aliaydin96/EngineeringDesign/Completed/Business Statement Report/CV's/NailTosunCV.pdf

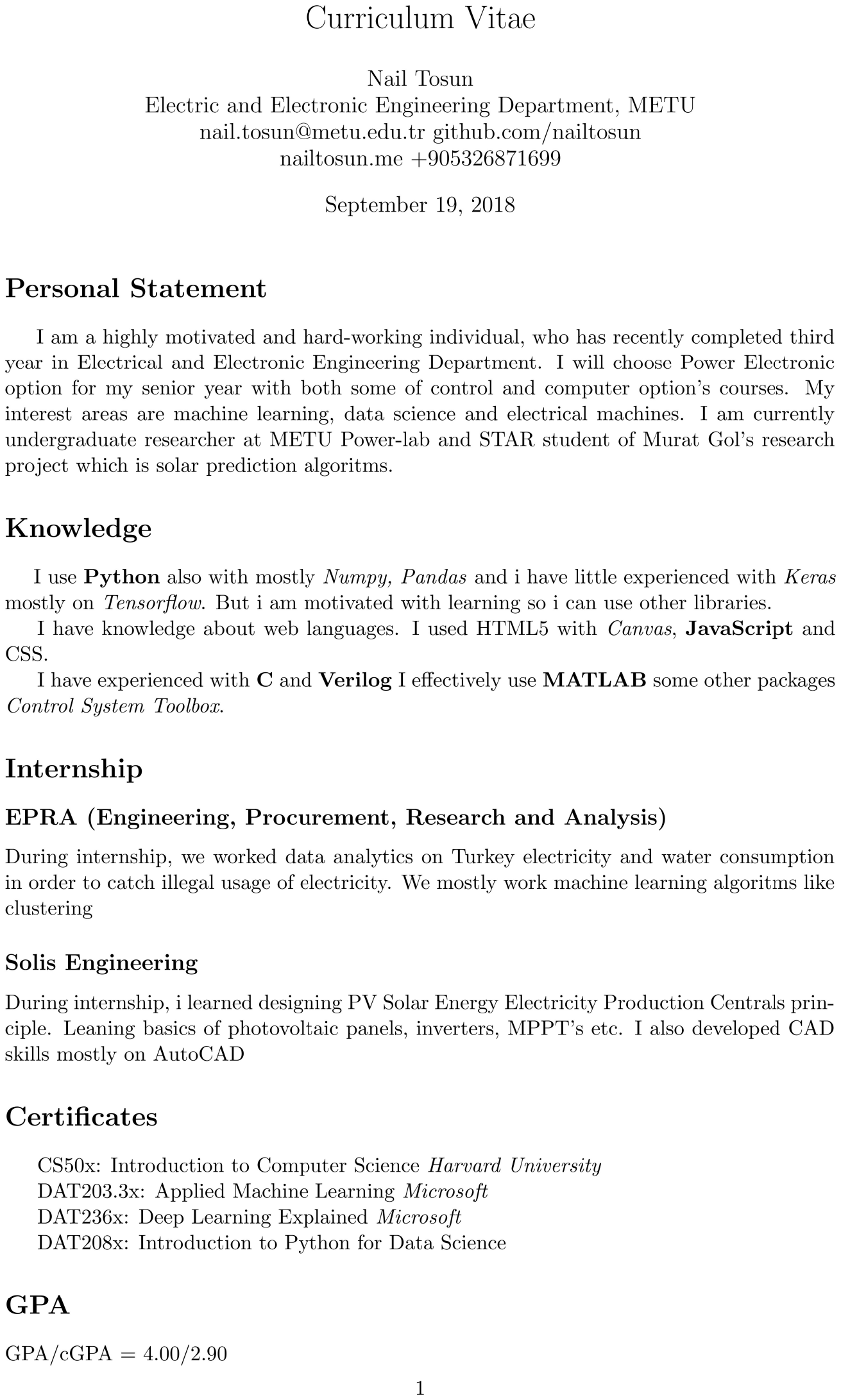
[picture p223: page 1]
