aliaydin96/EngineeringDesign/Algorithm/MappingV2/Mapping/Map.png

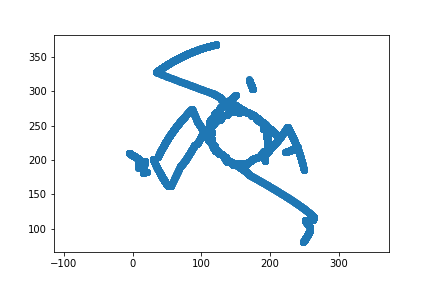
Algorithm/MappingV2/Mapping/Map.png
