aliaydin96/EngineeringDesign/Algorithm/Road Map/line1.PNG

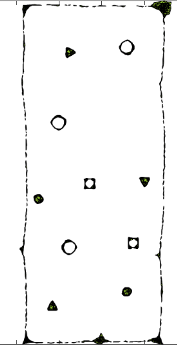
Algorithm/Road Map/line1.PNG
