aliaydin96/EngineeringDesign/Algorithm/Road Map/line.png

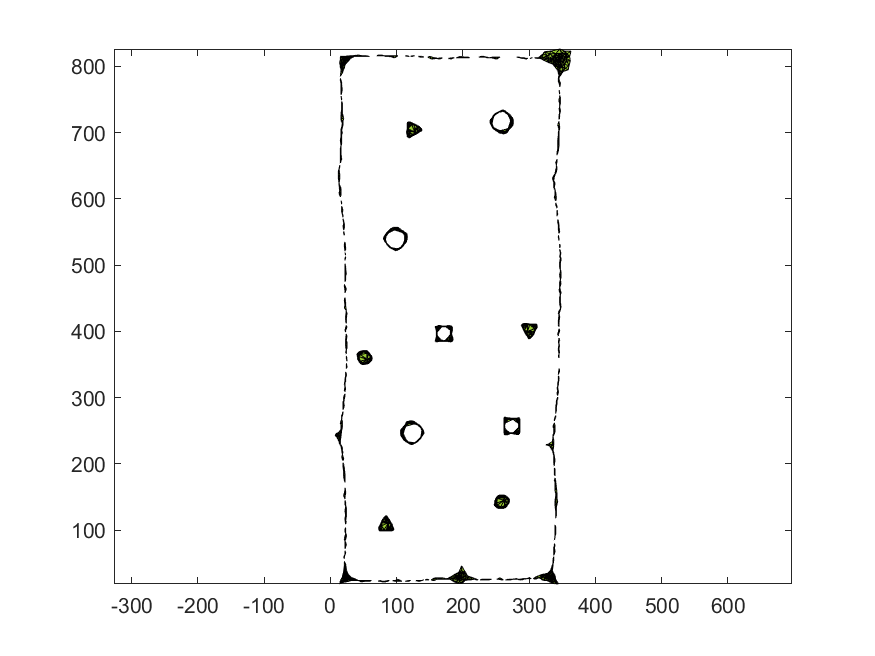
Algorithm/Road Map/line.png
