aliaydin96/EngineeringDesign/Algorithm/Road Map/Mapping_R/Mapping/Map.png

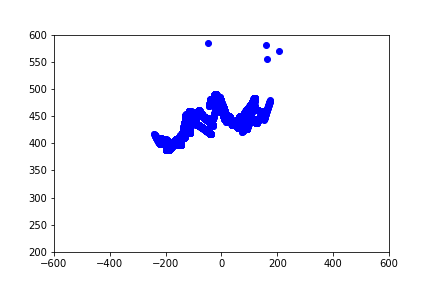
Algorithm/Road Map/Mapping_R/Mapping/Map.png
