aliaydin96/EngineeringDesign/Algorithm/RoadMapAlgroithm/Data1(Cleaning with average filter).png

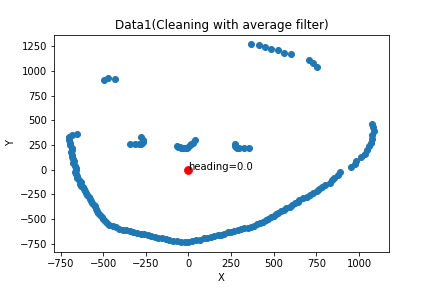
Algorithm/RoadMapAlgroithm/Data1(Cleaning with average filter).png
