aliaydin96/EngineeringDesign/Algorithm/route_determination/1.JPG

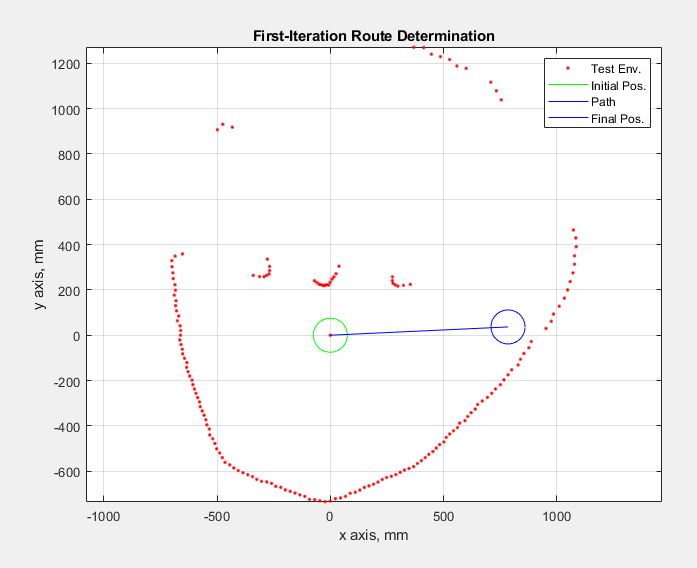
Algorithm/route_determination/1.JPG
