aliaydin96/EngineeringDesign/Algorithm/route_determination/2.JPG

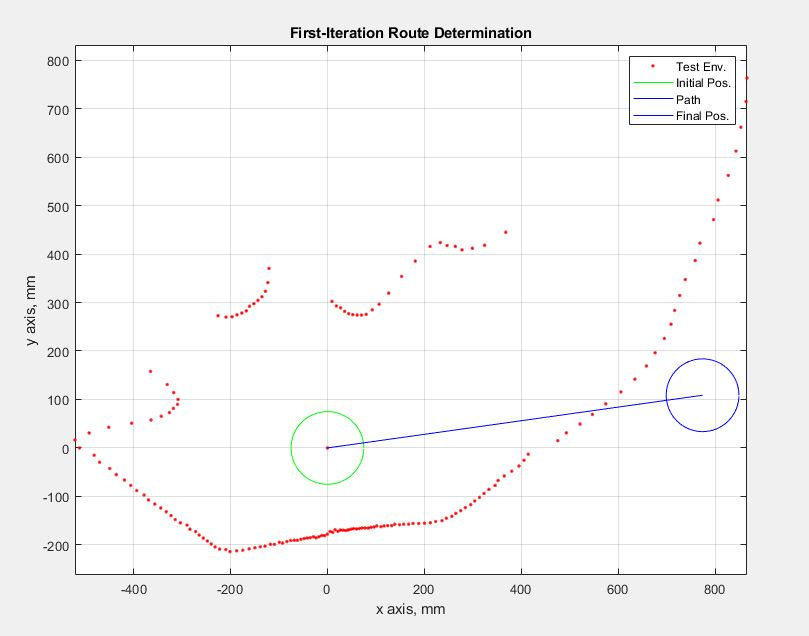
Algorithm/route_determination/2.JPG
