aliaydin96/EngineeringDesign/Algorithm/route_determination/3.JPG

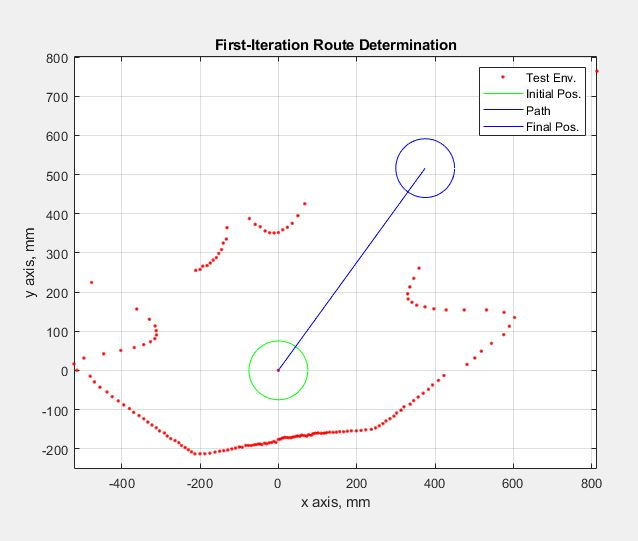
Algorithm/route_determination/3.JPG
