aliaydin96/EngineeringDesign/Algorithm/route_determination/4.JPG

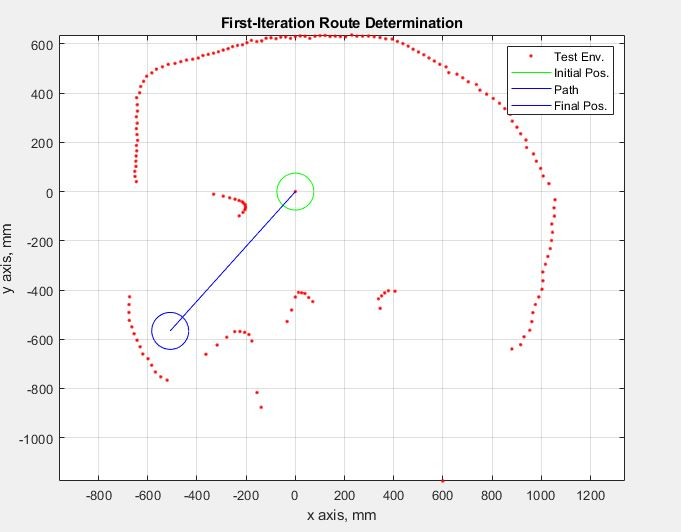
Algorithm/route_determination/4.JPG
