aliaydin96/EngineeringDesign/Algorithm/route_determination/5.JPG

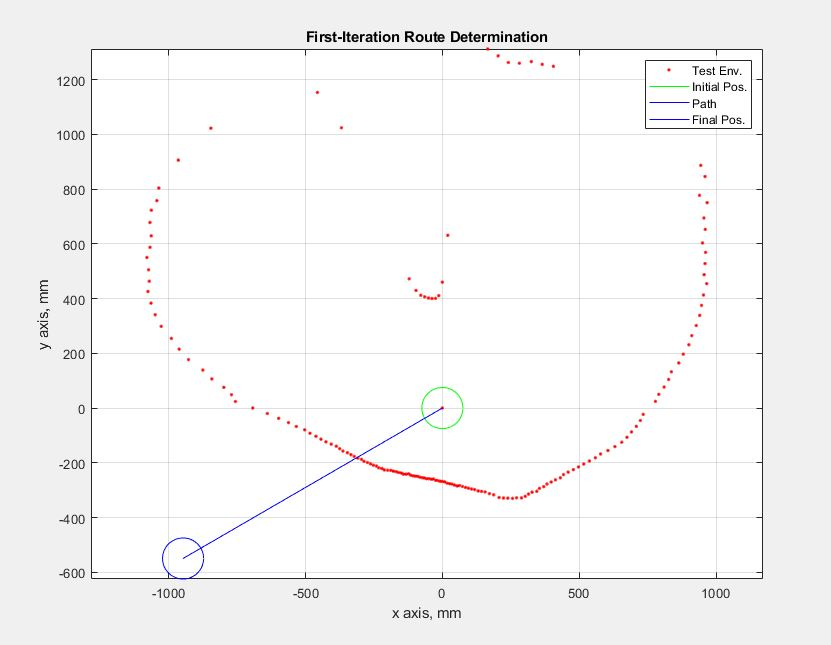
Algorithm/route_determination/5.JPG
