aliaydin96/EngineeringDesign/Algorithm/route_determination/6.JPG

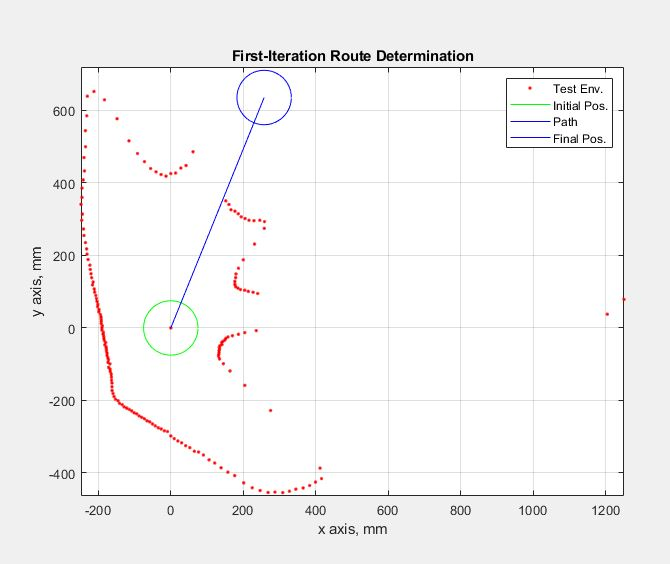
Algorithm/route_determination/6.JPG
