aliaydin96/EngineeringDesign/Algorithm/route_determination/7.JPG

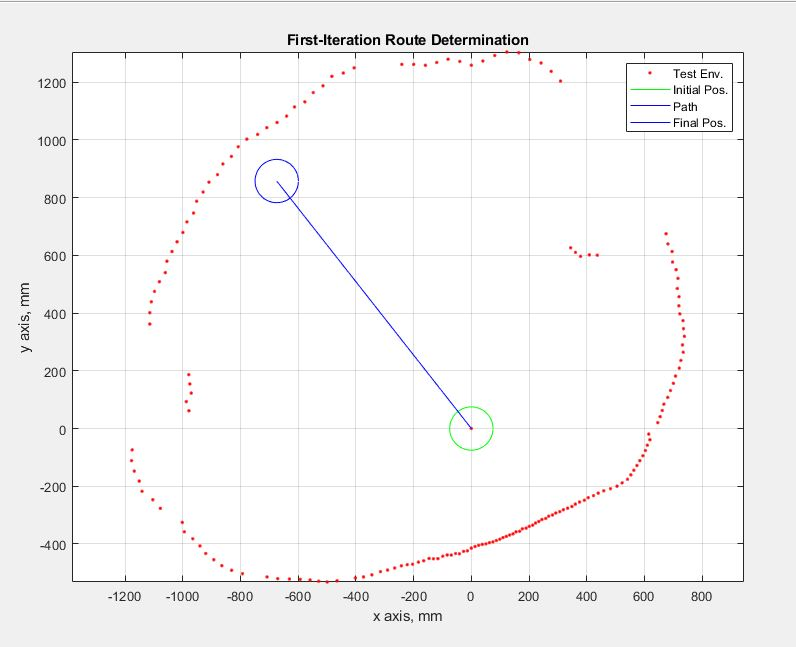
Algorithm/route_determination/7.JPG
