aliaydin96/EngineeringDesign/Algorithm/route_determination/8.JPG

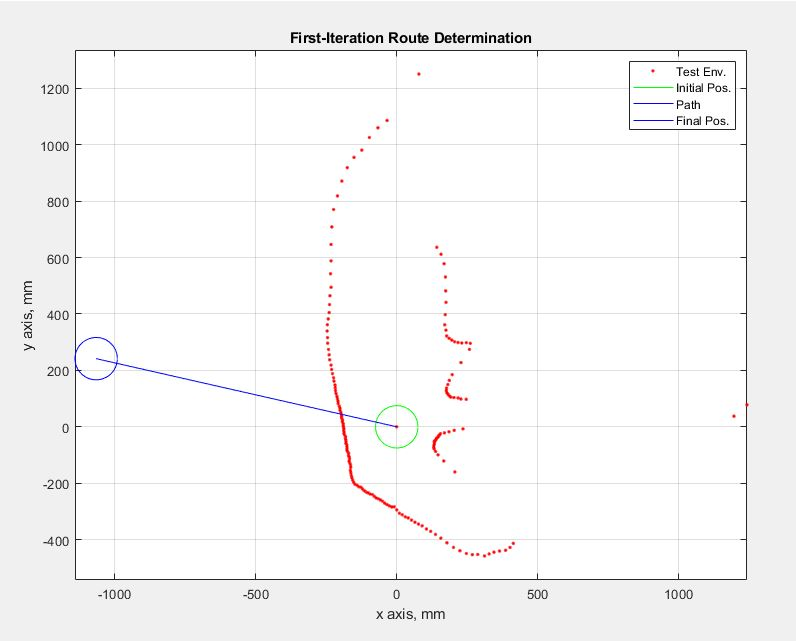
Algorithm/route_determination/8.JPG
