aliaydin96/EngineeringDesign/Algorithm/route_determination/9.JPG

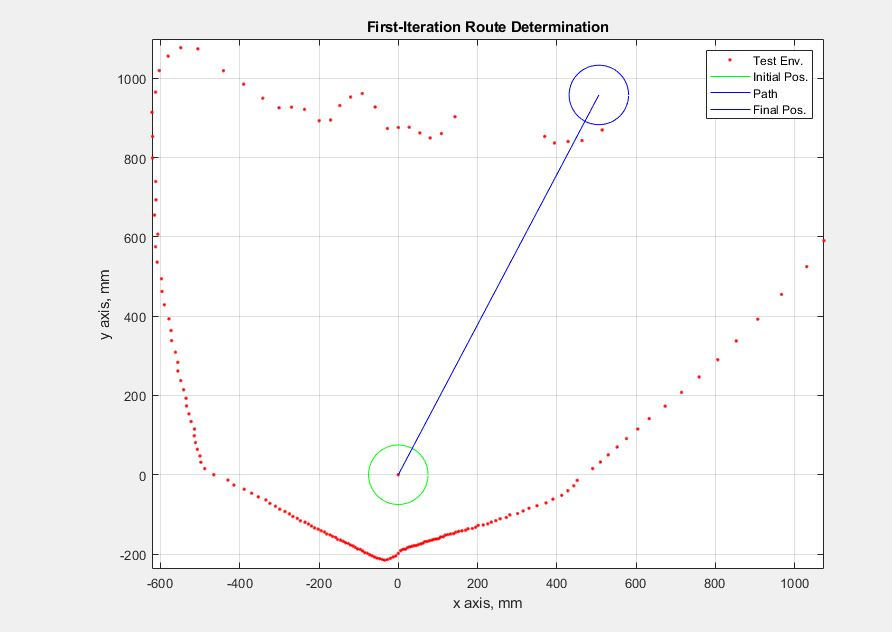
Algorithm/route_determination/9.JPG
