aliaydin96/EngineeringDesign/Algorithm/route_determination/Capture.JPG

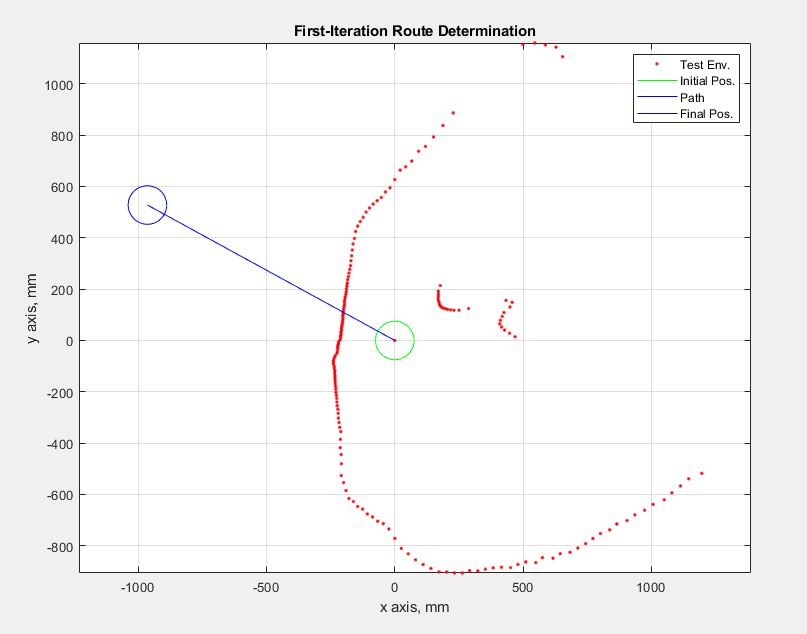
Algorithm/route_determination/Capture.JPG
