aliaydin96/EngineeringDesign/Algorithm/ShapeFinder/Matlab- Solid Shape/1.jpeg

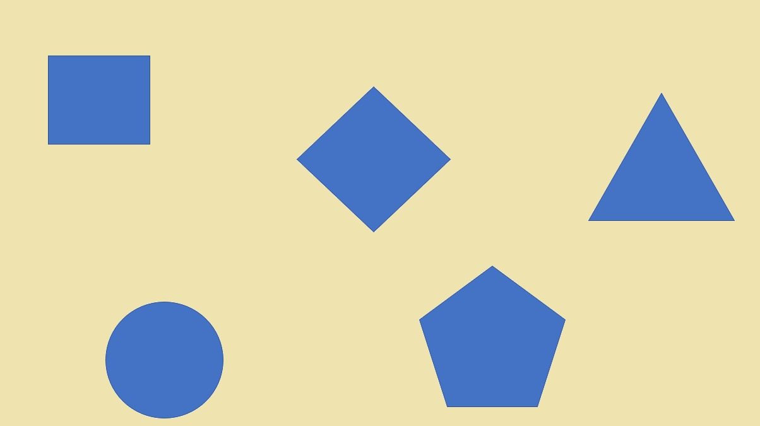
Algorithm/ShapeFinder/Matlab- Solid Shape/1.jpeg
