aliaydin96/EngineeringDesign/Algorithm/simulation_python_shape_center/outfile.jpg

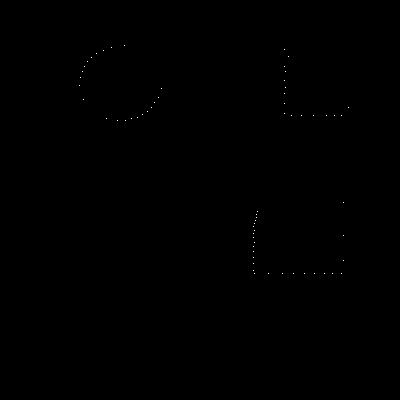
Algorithm/simulation_python_shape_center/outfile.jpg
