aliaydin96/EngineeringDesign/Completed/Business Statement Report/BS requirements.PNG

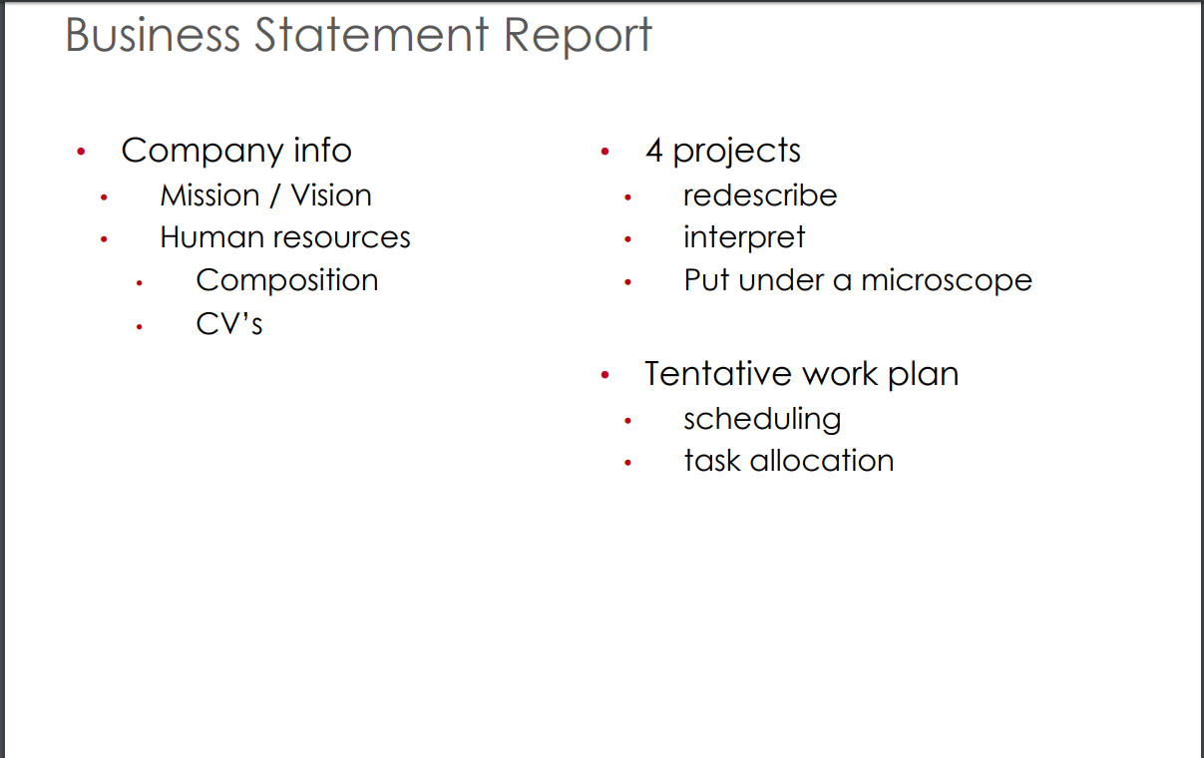
Completed/Business Statement Report/BS requirements.PNG
