aliaydin96/EngineeringDesign/Algorithm/measurement/data1.csv

0.000000000000000000e+00 | 9.100000000000000000e+02 | 9.040000000000000000e+02 | 9.120000000000000000e+02 | 9.130000000000000000e+02 | 9.080000000000000000e+02 | 9.200000000000000000e+02 | 9.360000000000000000e+02 | 9.480000000000000000e+02 | 9.350000000000000000e+02 | 9.620000000000000000e+02 | 9.800000000000000000e+02 | 9.920000000000000000e+02 | 1.005000000000000000e+03 | 1.010000000000000000e+03 | 1.016000000000000000e+03 | 1.040000000000000000e+03 | 1.050000000000000000e+03 | 1.073000000000000000e+03 | 1.088000000000000000e+03 | 1.115000000000000000e+03 | 1.121000000000000000e+03 | 1.142000000000000000e+03 | 1.183000000000000000e+03 | 1.193000000000000000e+03 | 1.230000000000000000e+03 | 1.240000000000000000e+03 | 1.251000000000000000e+03 | 1.265000000000000000e+03 | 1.284000000000000000e+03 | 1.269000000000000000e+03 | 1.295000000000000000e+03 | 1.290000000000000000e+03 | 1.300000000000000000e+03 | 1.305000000000000000e+03 | 1.305000000000000000e+03 | 1.289000000000000000e+03 | 1.318000000000000000e+03 | 1.306000000000000000e+03 | 1.312000000000000000e+03 | 1.301000000000000000e+03 | 1.287000000000000000e+03 | 1.274000000000000000e+03 | 1.250000000000000000e+03 |
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
