aliaydin96/EngineeringDesign/Algorithm/measurement/data2.csv

0.000000000000000000e+00 | 1.173000000000000000e+03 | 1.160000000000000000e+03 | 1.148000000000000000e+03 | 1.140000000000000000e+03 | 1.109000000000000000e+03 | 1.098000000000000000e+03 | 1.083000000000000000e+03 | 1.062000000000000000e+03 | 1.055000000000000000e+03 | 1.037000000000000000e+03 | 1.019000000000000000e+03 | 1.018000000000000000e+03 | 1.005000000000000000e+03 | 9.980000000000000000e+02 | 9.830000000000000000e+02 | 9.760000000000000000e+02 | 9.750000000000000000e+02 | 9.670000000000000000e+02 | 9.640000000000000000e+02 | 9.570000000000000000e+02 | 9.450000000000000000e+02 | 9.510000000000000000e+02 | 9.440000000000000000e+02 | 9.410000000000000000e+02 | 9.400000000000000000e+02 | 9.350000000000000000e+02 | 9.230000000000000000e+02 | 9.240000000000000000e+02 | 9.290000000000000000e+02 | 9.340000000000000000e+02 | 9.230000000000000000e+02 | 9.420000000000000000e+02 | 9.330000000000000000e+02 | 9.380000000000000000e+02 | 9.500000000000000000e+02 | 9.380000000000000000e+02 | 9.550000000000000000e+02 | 9.540000000000000000e+02 | 9.510000000000000000e+02 | 9.500000000000000000e+02 | 9.480000000000000000e+02 | 9.340000000000000000e+02 | 9.220000000000000000e+02 |
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
