aliaydin96/EngineeringDesign/Algorithm/measurement/data3.csv

0.000000000000000000e+00 | 9.320000000000000000e+02 | 9.140000000000000000e+02 | 9.010000000000000000e+02 | 8.730000000000000000e+02 | 8.510000000000000000e+02 | 8.480000000000000000e+02 | 8.340000000000000000e+02 | 8.200000000000000000e+02 | 8.090000000000000000e+02 | 7.960000000000000000e+02 | 7.930000000000000000e+02 | 7.760000000000000000e+02 | 7.630000000000000000e+02 | 7.510000000000000000e+02 | 7.440000000000000000e+02 | 7.310000000000000000e+02 | 7.240000000000000000e+02 | 7.140000000000000000e+02 | 7.070000000000000000e+02 | 6.960000000000000000e+02 | 6.990000000000000000e+02 | 6.890000000000000000e+02 | 6.880000000000000000e+02 | 6.870000000000000000e+02 | 6.780000000000000000e+02 | 6.780000000000000000e+02 | 6.700000000000000000e+02 | 6.690000000000000000e+02 | 6.660000000000000000e+02 | 6.760000000000000000e+02 | 6.710000000000000000e+02 | 6.730000000000000000e+02 | 6.700000000000000000e+02 | 6.710000000000000000e+02 | 6.680000000000000000e+02 | 6.570000000000000000e+02 | 6.570000000000000000e+02 | 6.450000000000000000e+02 | 6.370000000000000000e+02 | 6.250000000000000000e+02 | 6.220000000000000000e+02 | 6.140000000000000000e+02 | 6.050000000000000000e+02 |
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
