aliaydin96/EngineeringDesign/Algorithm/measurements_for selflocaliztion/harita1/data0.csv

0.000000000000000000e+00 | 7.550000000000000000e+02 | 7.720000000000000000e+02 | 8.000000000000000000e+02 | 8.160000000000000000e+02 | 8.340000000000000000e+02 | 8.500000000000000000e+02 | 8.970000000000000000e+02 | 9.010000000000000000e+02 | 9.350000000000000000e+02 | 9.550000000000000000e+02 | 9.860000000000000000e+02 | 1.010000000000000000e+03 | 1.023000000000000000e+03 | 1.030000000000000000e+03 | 1.057000000000000000e+03 | 1.076000000000000000e+03 | 1.087000000000000000e+03 | 1.113000000000000000e+03 | 1.137000000000000000e+03 | 1.135000000000000000e+03 | 1.156000000000000000e+03 | 1.159000000000000000e+03 | 1.171000000000000000e+03 | 1.187000000000000000e+03 | 1.201000000000000000e+03 | 1.201000000000000000e+03 | 1.215000000000000000e+03 | 1.217000000000000000e+03 | 1.225000000000000000e+03 | 1.254000000000000000e+03 | 1.269000000000000000e+03 | 1.274000000000000000e+03 | 1.300000000000000000e+03 | 1.297000000000000000e+03 | 1.308000000000000000e+03 | 1.323000000000000000e+03 | 8.242000000000000000e+03 | 8.242000000000000000e+03 | 8.242000000000000000e+03 | 8.242000000000000000e+03 | 8.242000000000000000e+03 | 8.242000000000000000e+03 | 8.242000000000000000e+03 |
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
