aliaydin96/EngineeringDesign/Algorithm/measurements_for selflocaliztion/harita1/data1.csv

0.000000000000000000e+00 | 8.330000000000000000e+02 | 8.500000000000000000e+02 | 8.590000000000000000e+02 | 8.790000000000000000e+02 | 8.960000000000000000e+02 | 9.190000000000000000e+02 | 9.320000000000000000e+02 | 9.380000000000000000e+02 | 9.460000000000000000e+02 | 9.560000000000000000e+02 | 9.710000000000000000e+02 | 9.710000000000000000e+02 | 9.810000000000000000e+02 | 9.920000000000000000e+02 | 1.005000000000000000e+03 | 1.007000000000000000e+03 | 1.026000000000000000e+03 | 1.025000000000000000e+03 | 1.033000000000000000e+03 | 1.049000000000000000e+03 | 1.048000000000000000e+03 | 1.057000000000000000e+03 | 1.072000000000000000e+03 | 1.048000000000000000e+03 | 1.054000000000000000e+03 | 1.083000000000000000e+03 | 1.067000000000000000e+03 | 1.090000000000000000e+03 | 1.092000000000000000e+03 | 1.105000000000000000e+03 | 1.109000000000000000e+03 | 1.121000000000000000e+03 | 1.129000000000000000e+03 | 1.143000000000000000e+03 | 1.154000000000000000e+03 | 1.147000000000000000e+03 | 1.153000000000000000e+03 | 1.170000000000000000e+03 | 1.185000000000000000e+03 | 1.194000000000000000e+03 | 1.196000000000000000e+03 | 1.213000000000000000e+03 | 1.211000000000000000e+03 |
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
