aliaydin96/EngineeringDesign/Algorithm/Environment Sensing Unit/a_successive_result_from_two_different_measurements.JPG

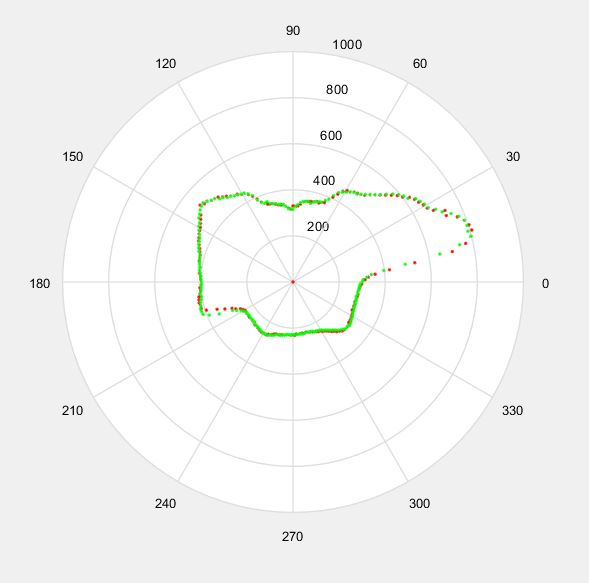
Algorithm/Environment Sensing Unit/a_successive_result_from_two_different_measurements.JPG
