aliaydin96/EngineeringDesign/Algorithm/measurement/before_filtering.JPG

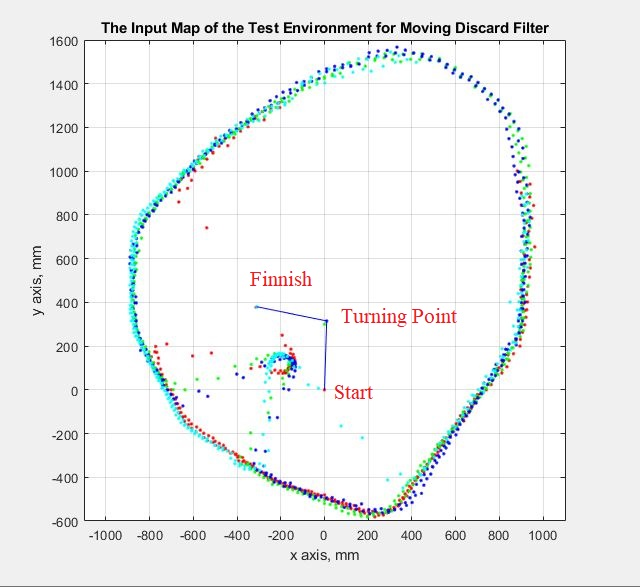
Algorithm/measurement/before_filtering.JPG
