aliaydin96/EngineeringDesign/Algorithm/measurement/filtered_map.JPG

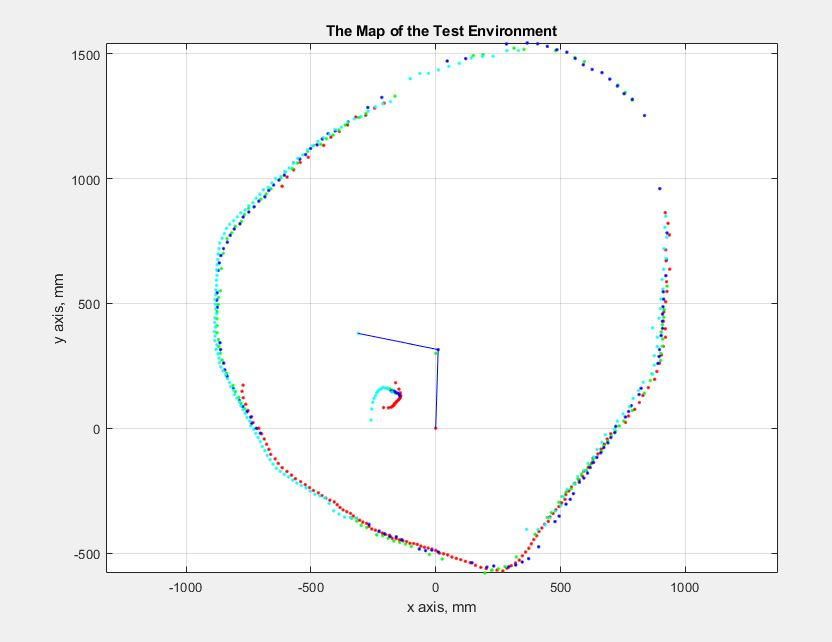
Algorithm/measurement/filtered_map.JPG
