aliaydin96/EngineeringDesign/Algorithm/measurements/cylinder_cartesian.JPG

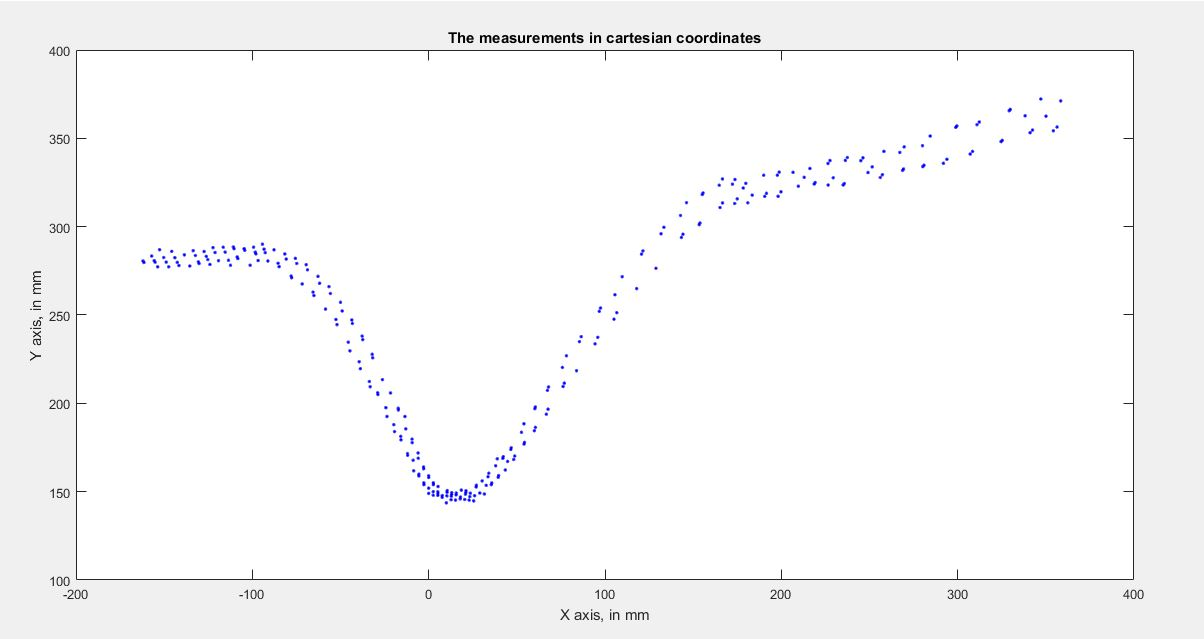
Algorithm/measurements/cylinder_cartesian.JPG
