aliaydin96/EngineeringDesign/Algorithm/measurements/cylinder_polar.JPG

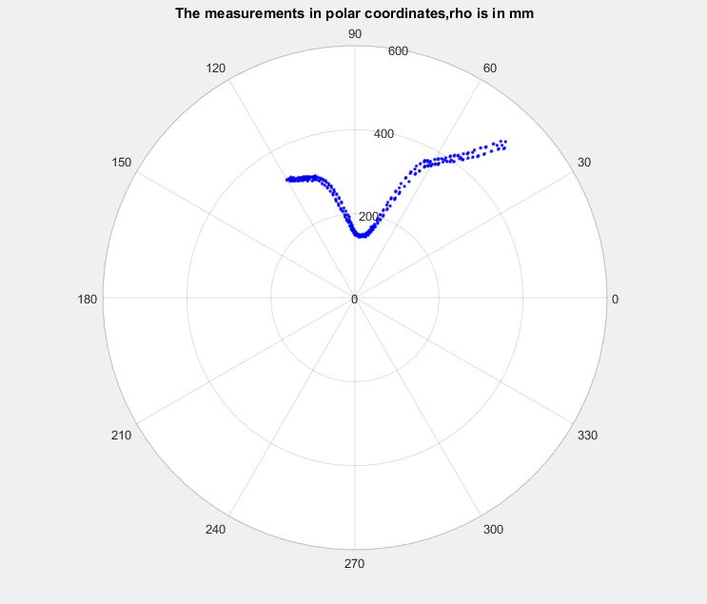
Algorithm/measurements/cylinder_polar.JPG
