aliaydin96/EngineeringDesign/Algorithm/measurements/triangular_cartesian.JPG

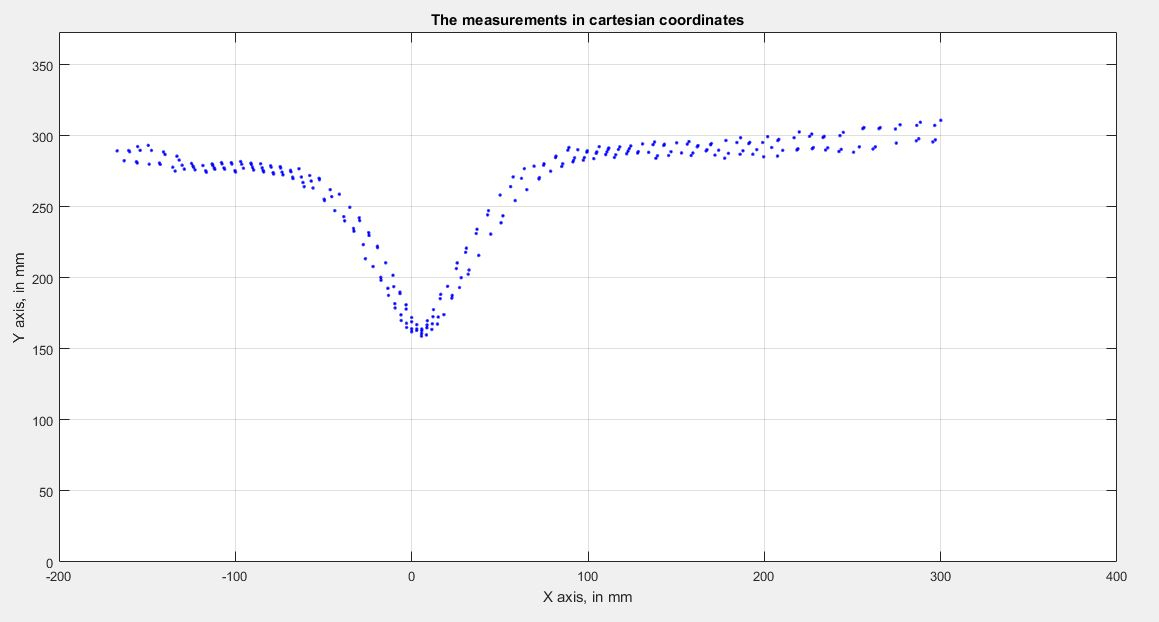
Algorithm/measurements/triangular_cartesian.JPG
