aliaydin96/EngineeringDesign/Algorithm/measurements/triangular_polar.JPG

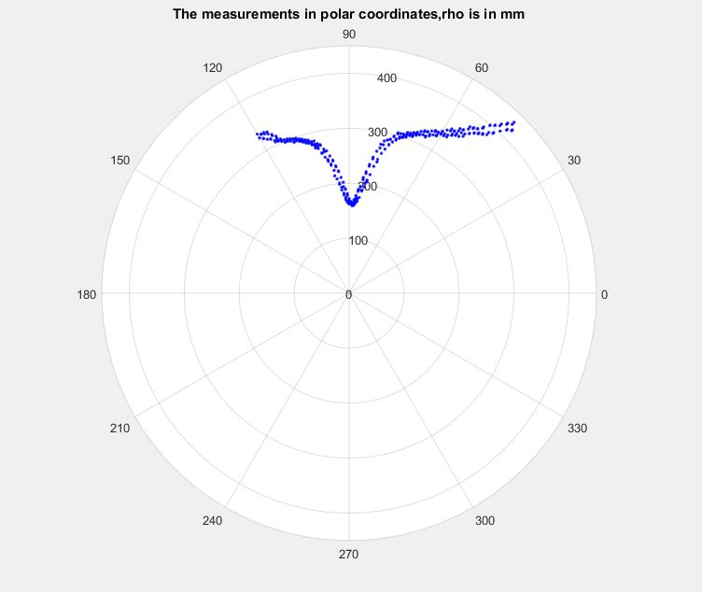
Algorithm/measurements/triangular_polar.JPG
