aliaydin96/EngineeringDesign/Algorithm/measurements_for selflocaliztion/harita2.JPG

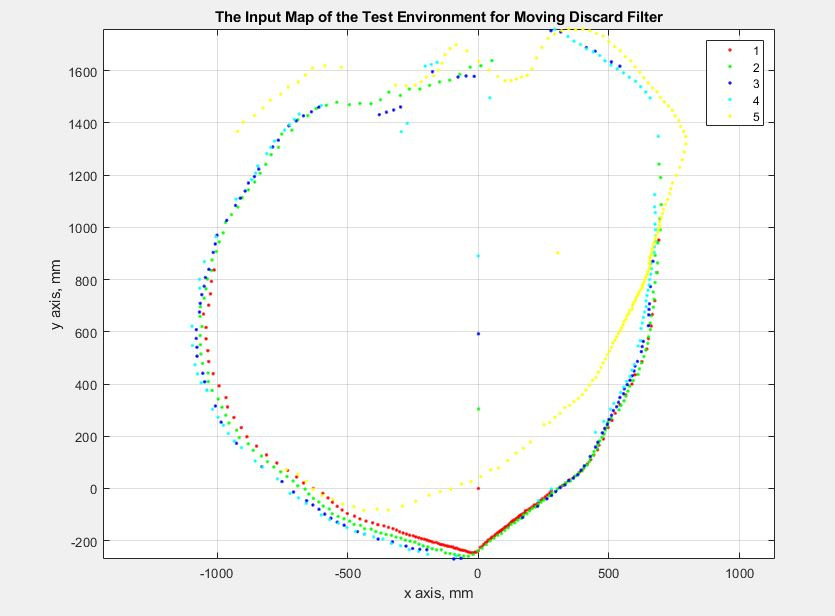
Algorithm/measurements_for selflocaliztion/harita2.JPG
