aliaydin96/EngineeringDesign/Algorithm/measurements_for selflocaliztion/harita3.JPG

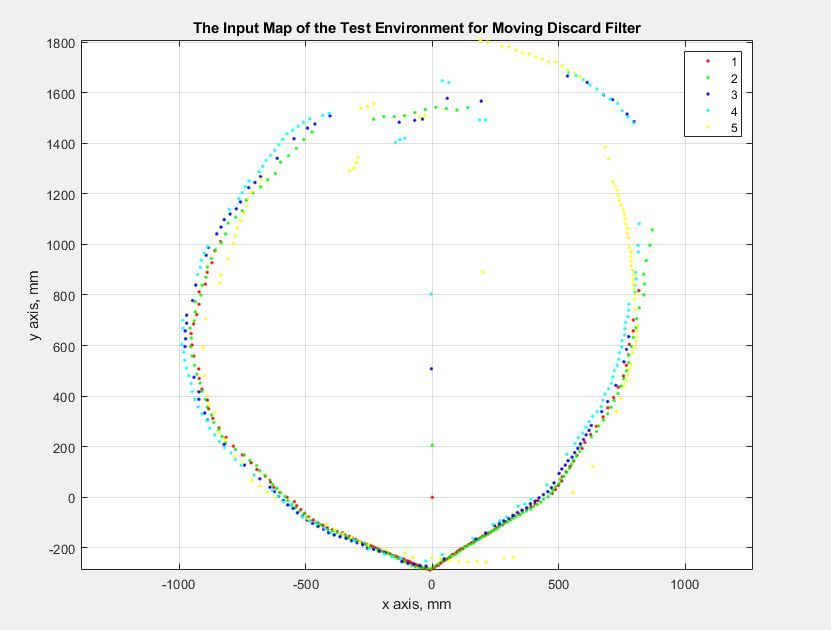
Algorithm/measurements_for selflocaliztion/harita3.JPG
