aliaydin96/EngineeringDesign/Algorithm/Road Map/test_plane.png

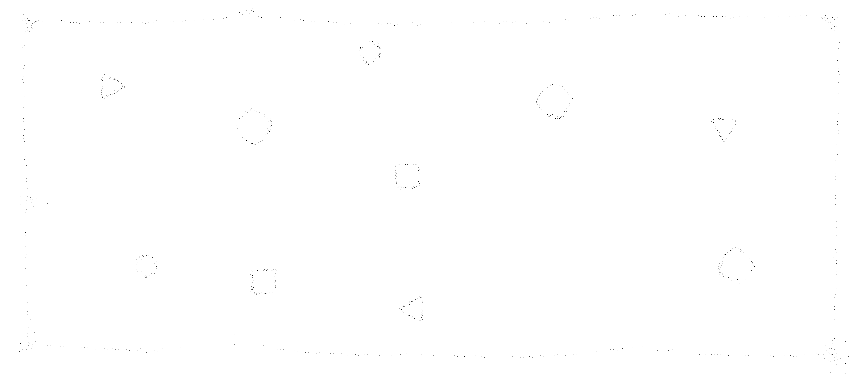
Algorithm/Road Map/test_plane.png
