aliaydin96/EngineeringDesign/Algorithm/RoadMapAlgroithm/Data1( Purely Measurement).png

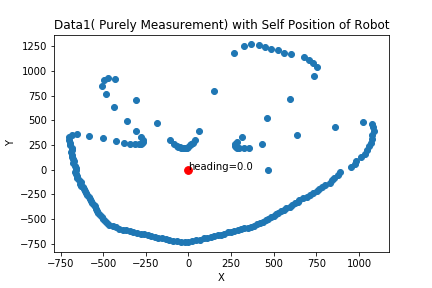
Algorithm/RoadMapAlgroithm/Data1( Purely Measurement).png
