aliaydin96/EngineeringDesign/Algorithm/ShapeFinder/Python-OpenCV-CounterNumber/test_file/test_2.png

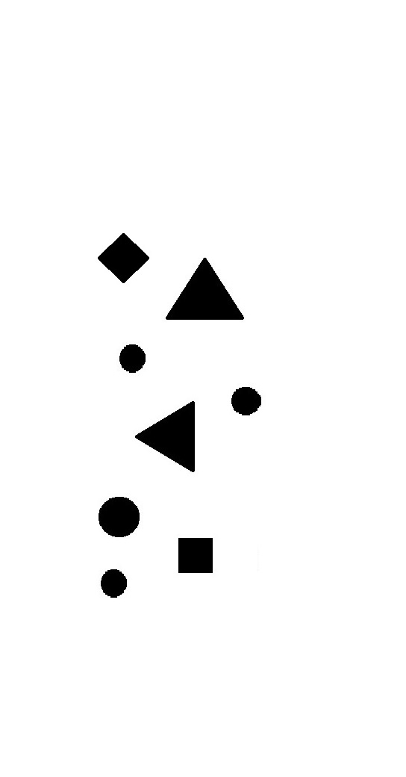
Algorithm/ShapeFinder/Python-OpenCV-CounterNumber/test_file/test_2.png
