aliaydin96/EngineeringDesign/Algorithm/ShapeFinder/Python-OpenCV-CounterNumber/test_file/test_5.png

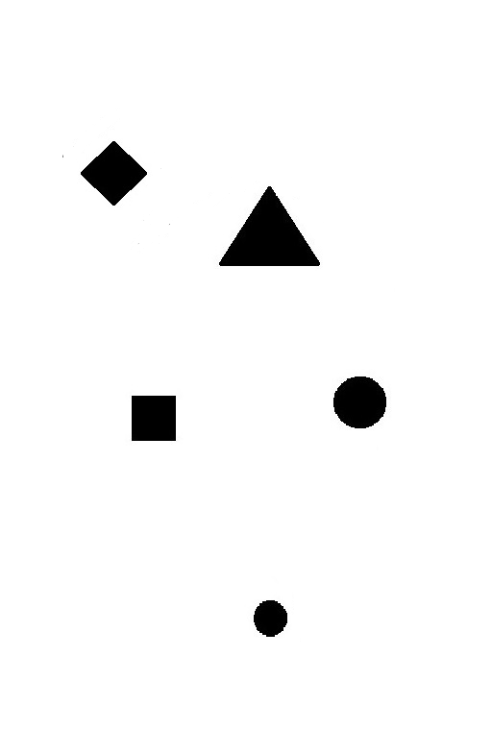
Algorithm/ShapeFinder/Python-OpenCV-CounterNumber/test_file/test_5.png
