aliaydin96/EngineeringDesign/Algorithm/test_palanes_with_real_measurements/test_plane_3.png

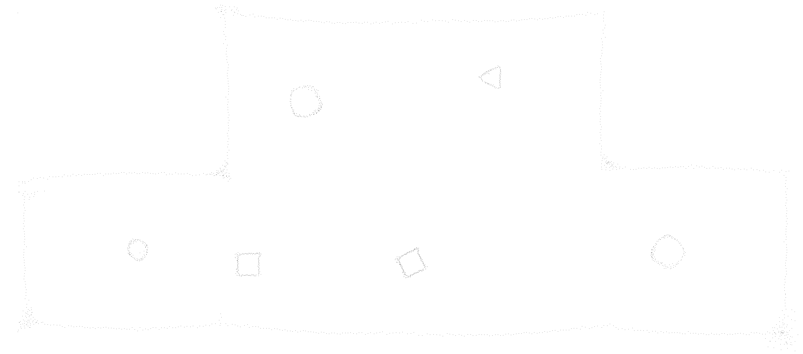
Algorithm/test_palanes_with_real_measurements/test_plane_3.png
