aliaydin96/EngineeringDesign/Algorithm/test_planes/test_1.JPG

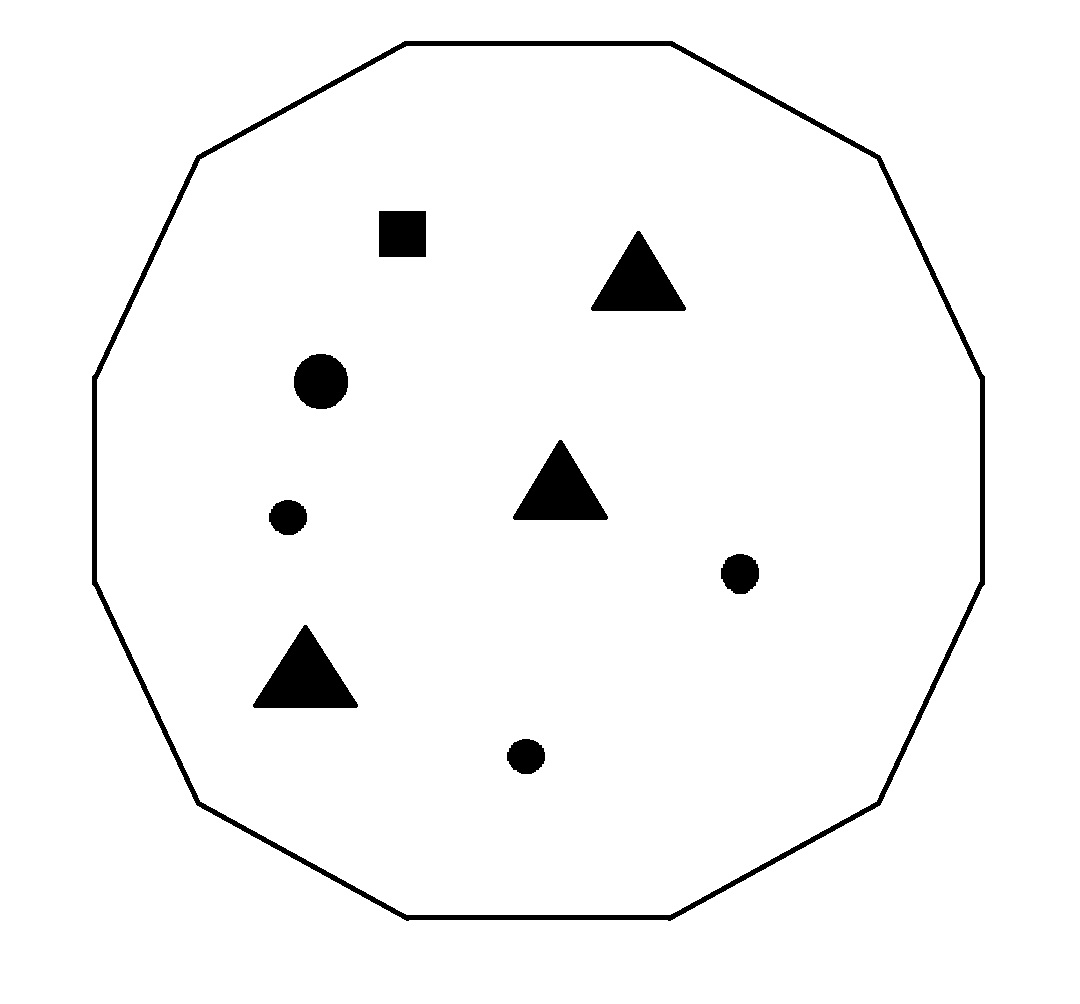
Algorithm/test_planes/test_1.JPG
