aliaydin96/EngineeringDesign/Algorithm/test_planes/test_2.JPG

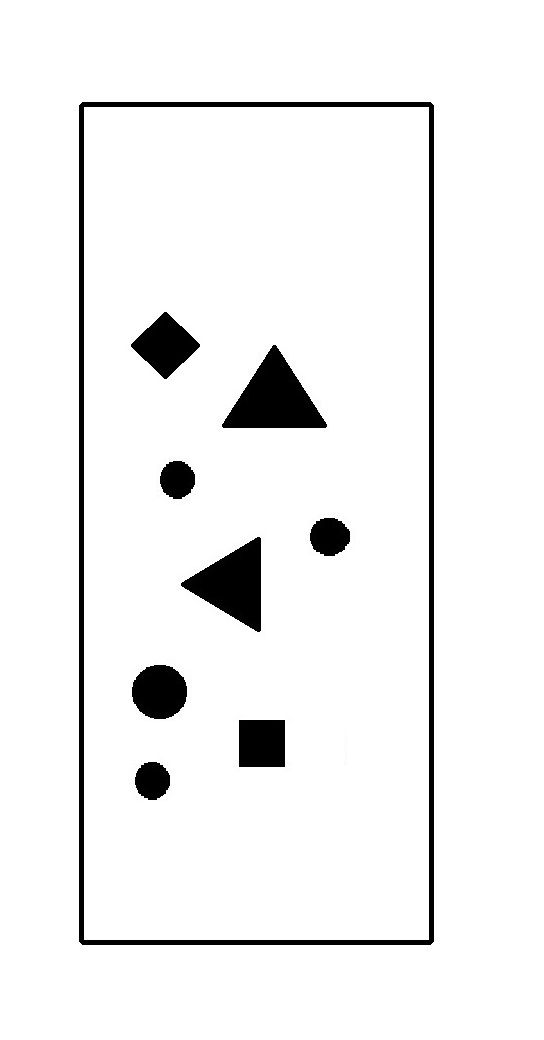
Algorithm/test_planes/test_2.JPG
