aliaydin96/EngineeringDesign/Algorithm/test_planes/test_4.JPG

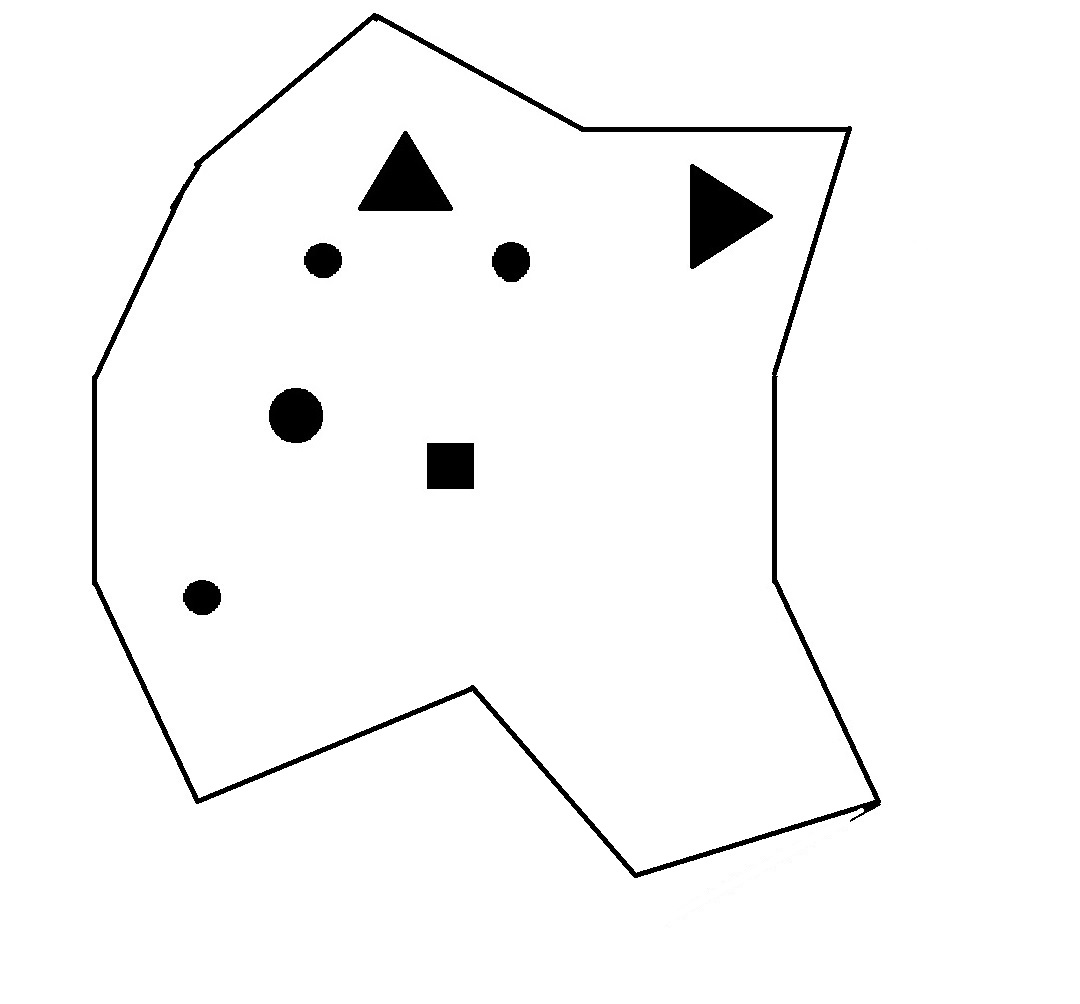
Algorithm/test_planes/test_4.JPG
