aliaydin96/EngineeringDesign/Algorithm/test_planes/test_5.JPG

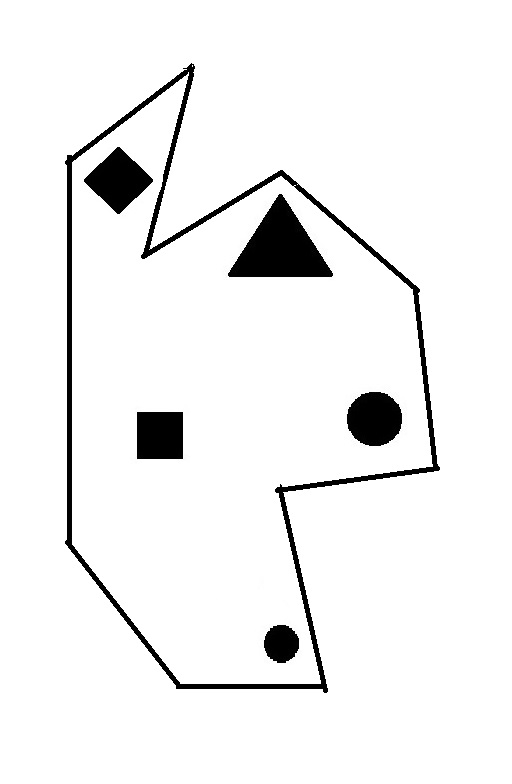
Algorithm/test_planes/test_5.JPG
