aliaydin96/EngineeringDesign/Algorithm/test_planes/test_6.JPG

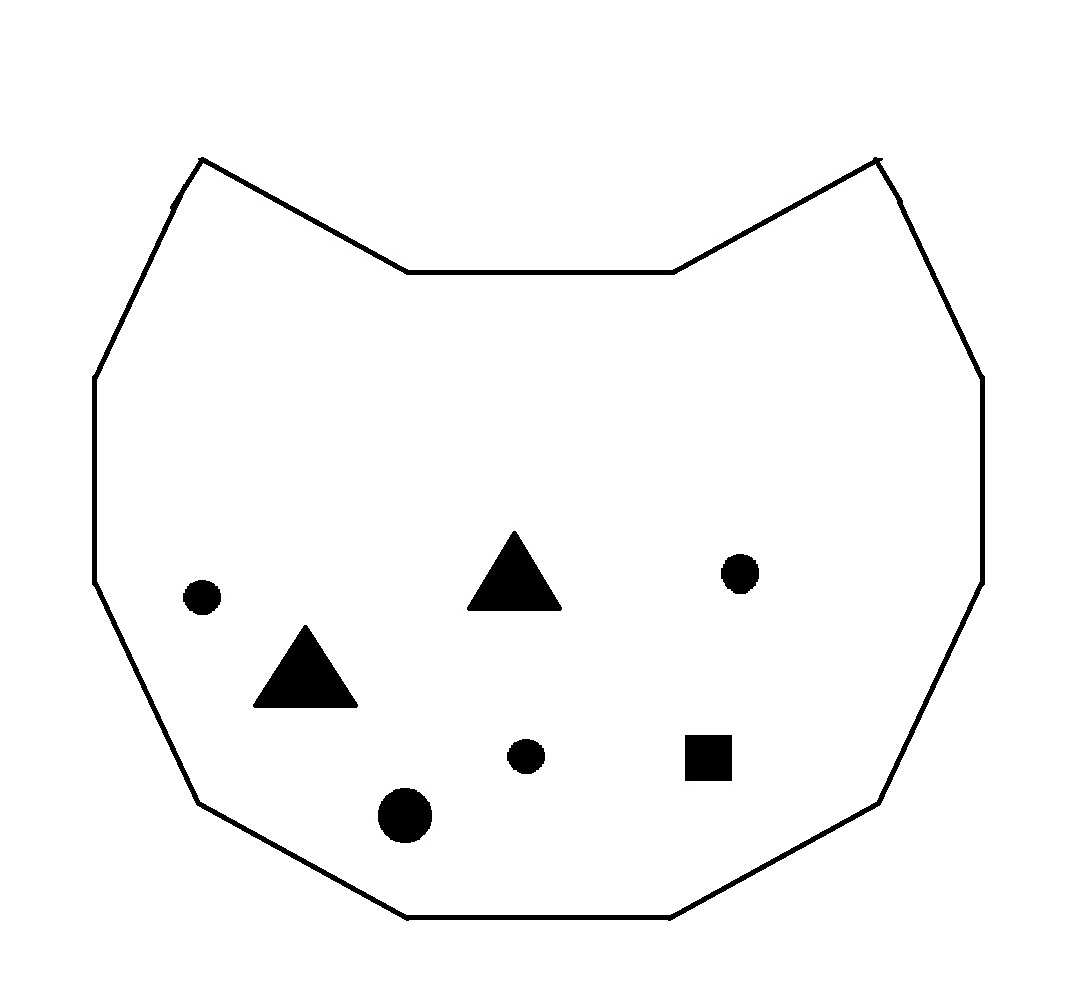
Algorithm/test_planes/test_6.JPG
