aliaydin96/EngineeringDesign/Algorithm/test_planes/test_7.JPG

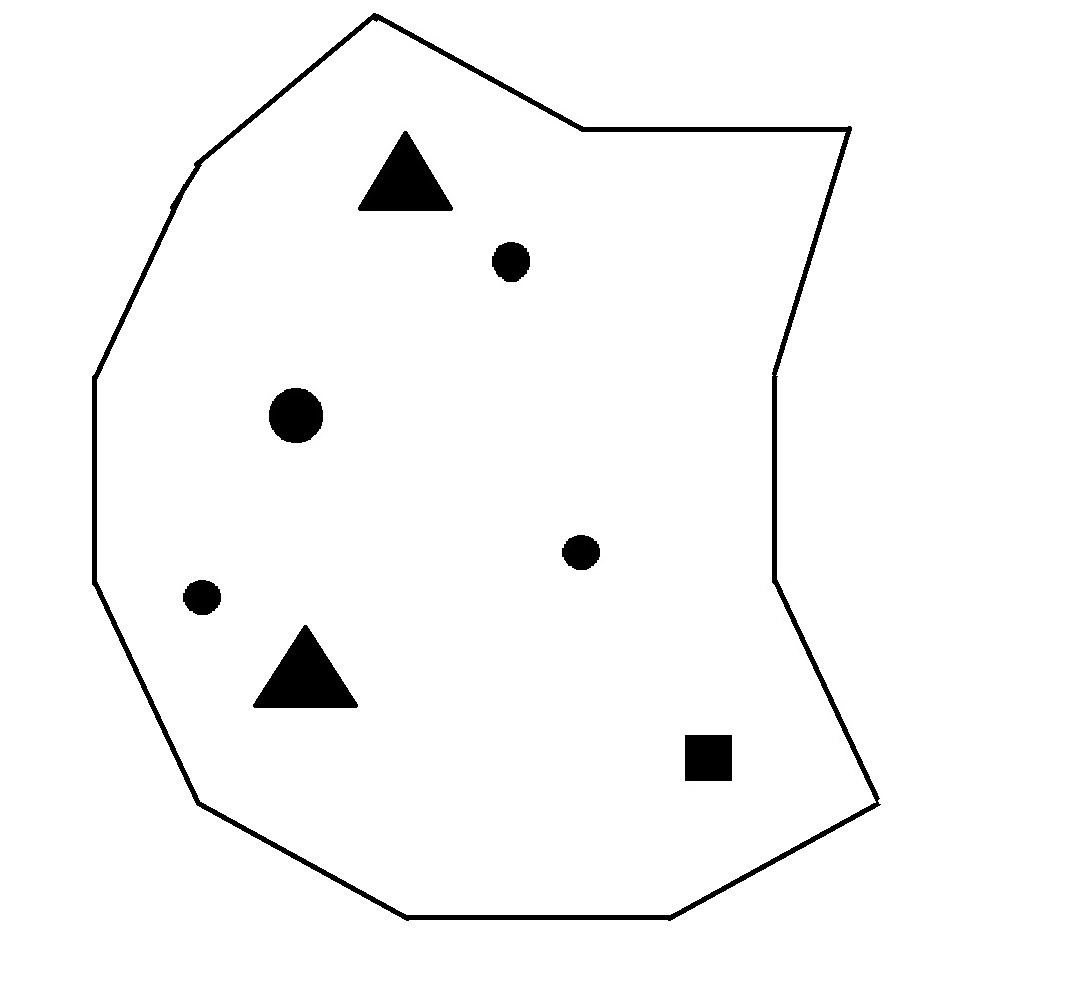
Algorithm/test_planes/test_7.JPG
