aliaydin96/EngineeringDesign/CDRR/Block Dİagram.pdf

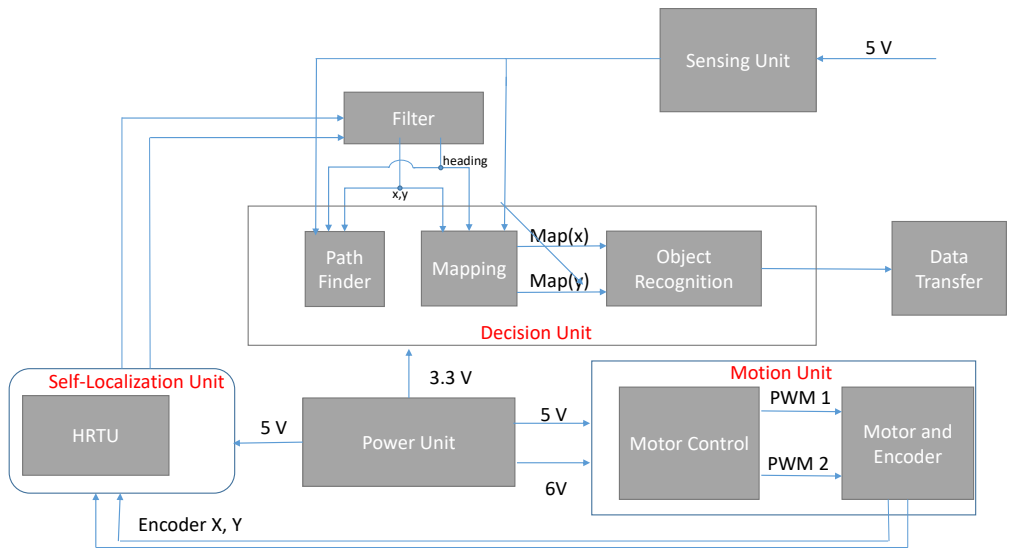
[picture p354: page 1]
Data Transfer; Object; Sensing Unit; HRTU; Motor Control; Motor and; Encoder; Filter; Map(x); Map(y); heading; Decision Unit; PWM 1; PWM 2; Encoder X, Y; Power Unit

Recognition Mapping Path
Finder

Motion Unit Self-Localization Unit
